shankarnandhini/Smart-Water-Quality-Monitoring-System/Mobile Application/Screenshot from 2023-11-15 15-45-07.png

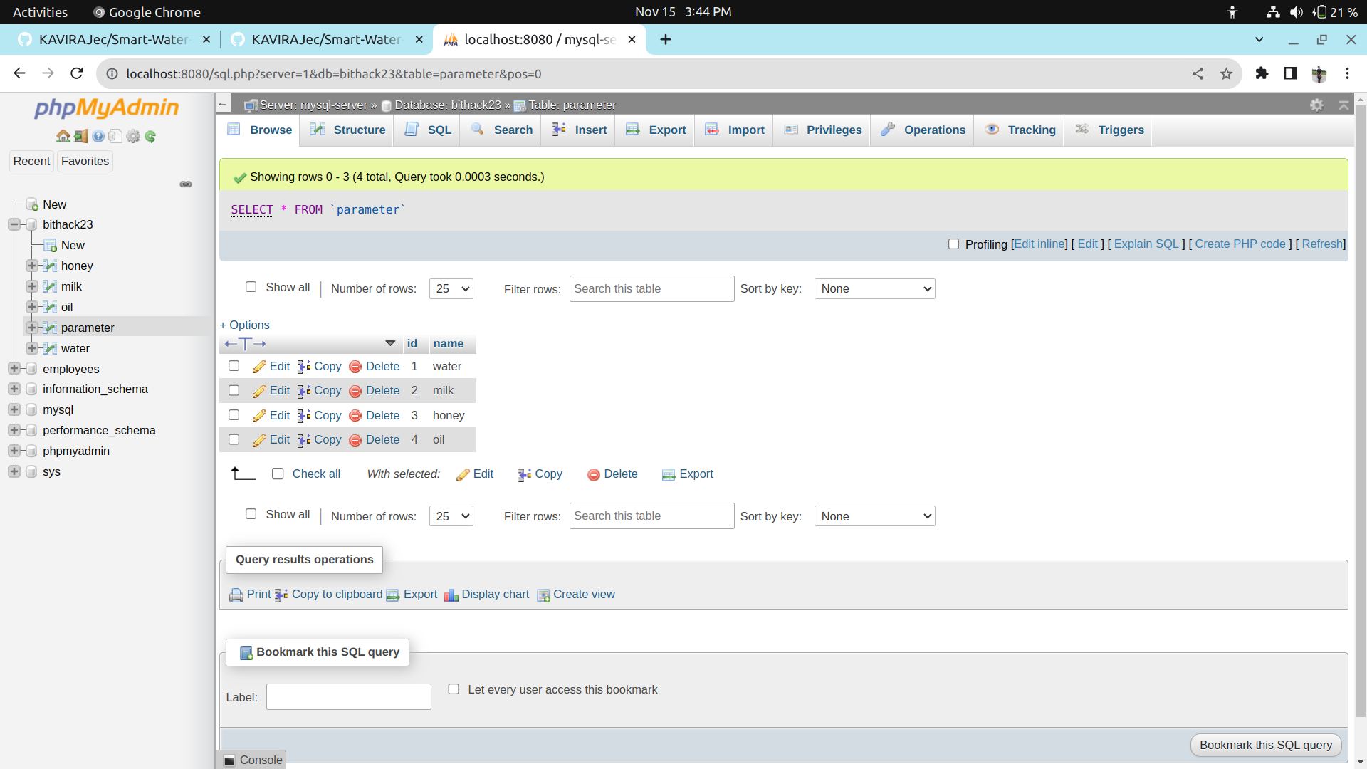
Mobile Application/Screenshot from 2023-11-15 15-45-07.png
