shankarnandhini/Smart-Water-Quality-Monitoring-System/Product image/IMG-20231110-WA0004.jpg

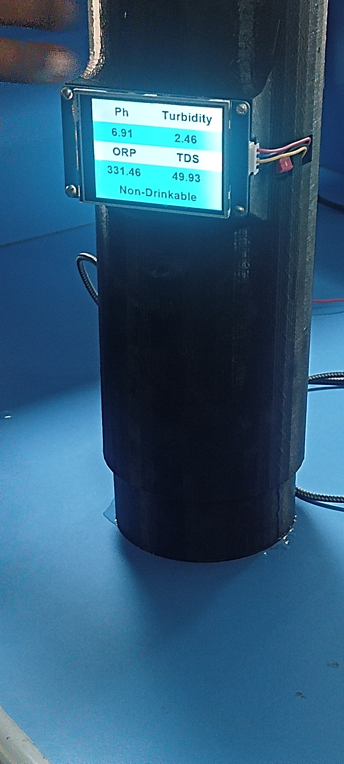
Product image/IMG-20231110-WA0004.jpg
