shankarnandhini/Smart-Water-Quality-Monitoring-System/Product image/IMG_20231109_144020.jpg

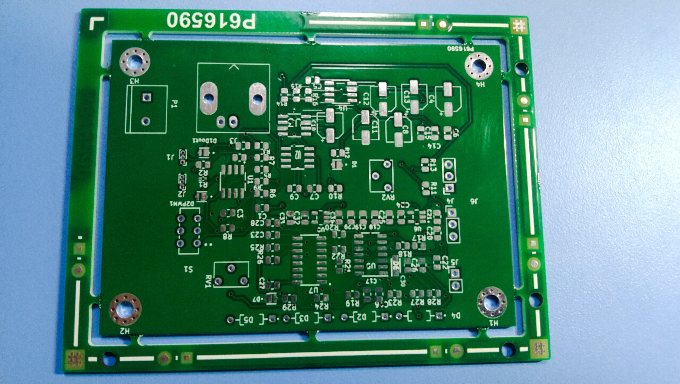
Product image/IMG_20231109_144020.jpg
