shankarnandhini/Smart-Water-Quality-Monitoring-System/Product image/IMG_20231109_144030.jpg

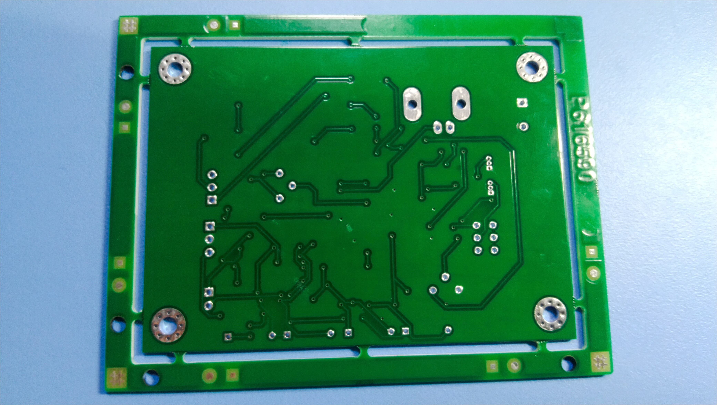
Product image/IMG_20231109_144030.jpg
