shankarnandhini/Smart-Water-Quality-Monitoring-System/Product image/IMG_20231110_140540_792.jpg

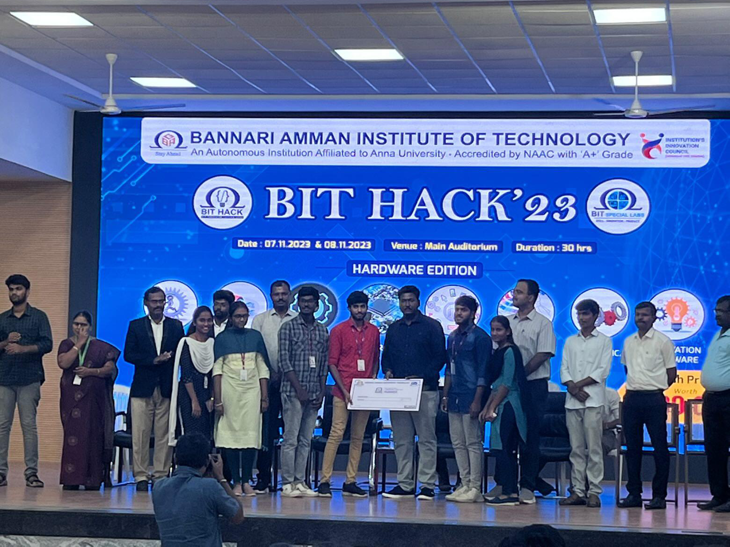
Product image/IMG_20231110_140540_792.jpg
